MasterEvarior/plantochi/docs/images/dump/20260617_101139.jpg

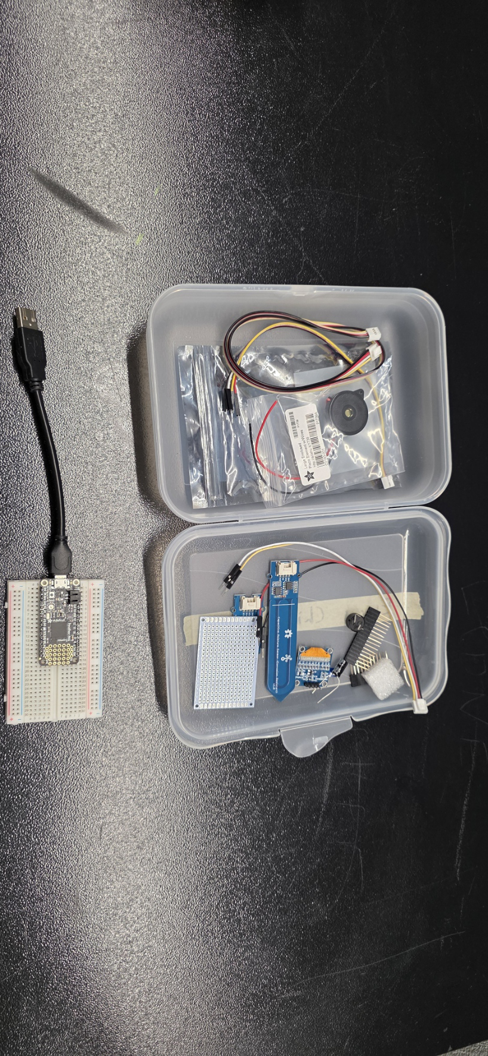
docs/images/dump/20260617_101139.jpg
