MasterEvarior/plantochi/docs/images/dump/20260617_101227.jpg

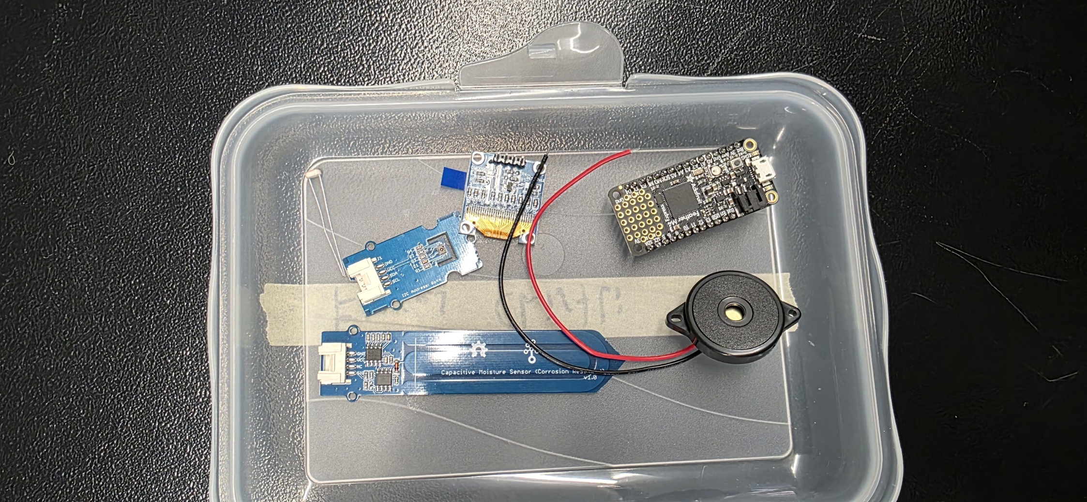
docs/images/dump/20260617_101227.jpg
