MasterEvarior/plantochi/docs/images/dump/20260617_132728.jpg

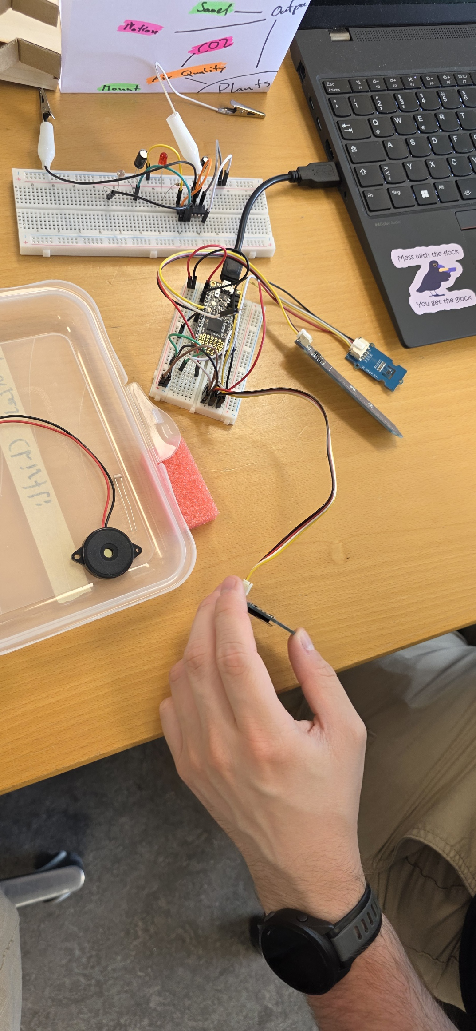
docs/images/dump/20260617_132728.jpg
