MasterEvarior/plantochi/docs/images/dump/20260617_132730.jpg

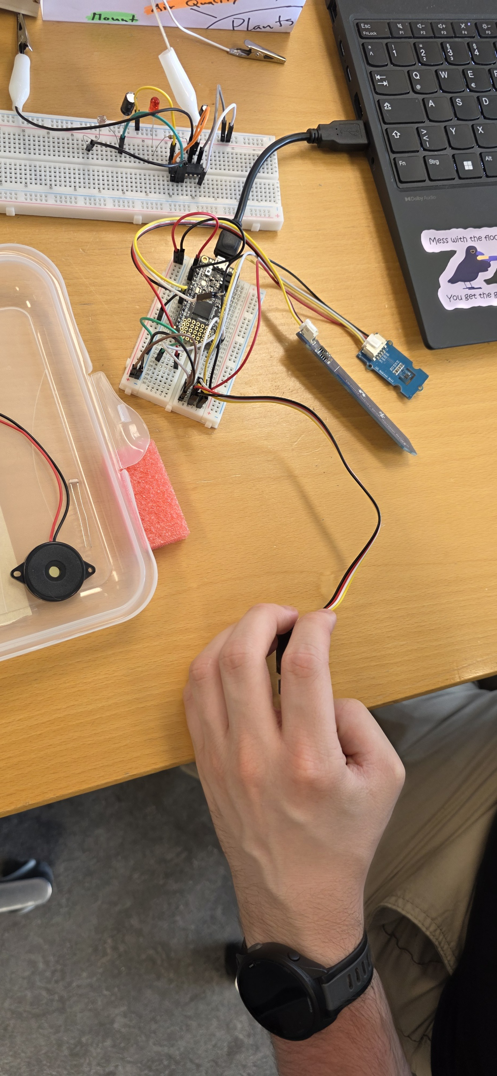
docs/images/dump/20260617_132730.jpg
