MasterEvarior/plantochi/docs/images/dump/20260617_132737.jpg

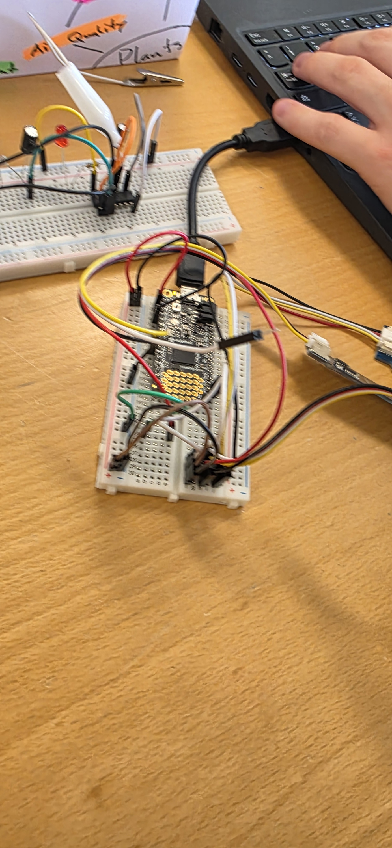
docs/images/dump/20260617_132737.jpg
