MasterEvarior/plantochi/docs/images/dump/20260617_132742.jpg

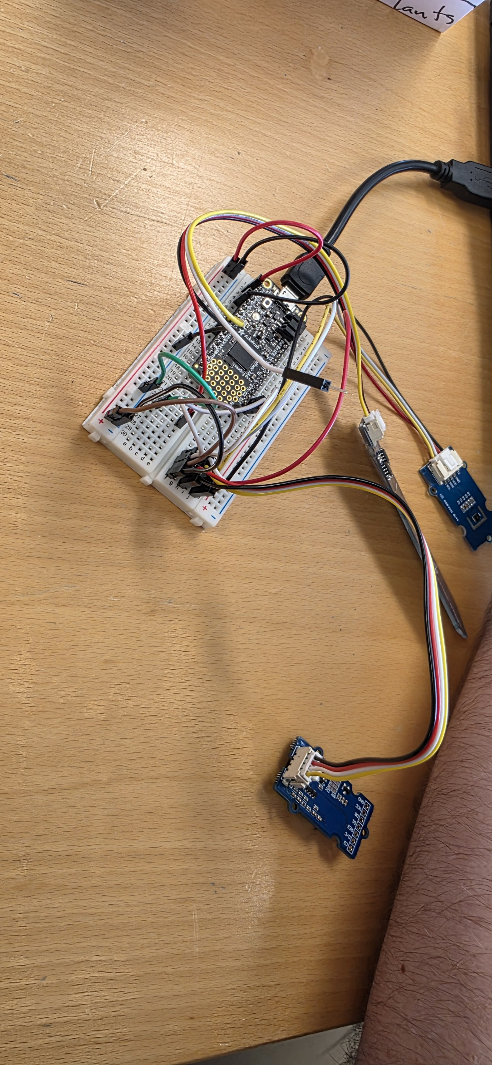
docs/images/dump/20260617_132742.jpg
