MasterEvarior/plantochi/docs/images/dump/20260617_134502.jpg

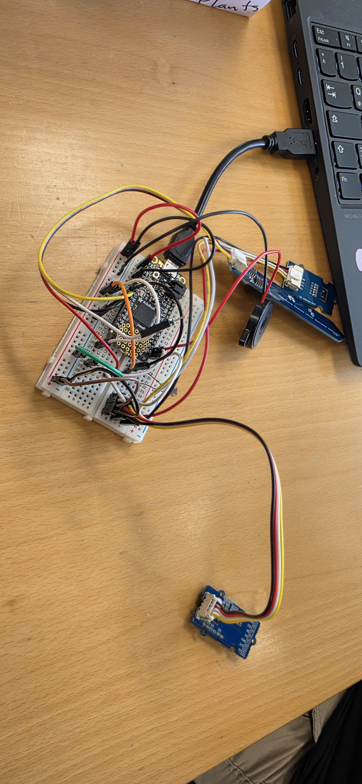
docs/images/dump/20260617_134502.jpg
