MasterEvarior/plantochi/docs/images/dump/20260617_134507.jpg

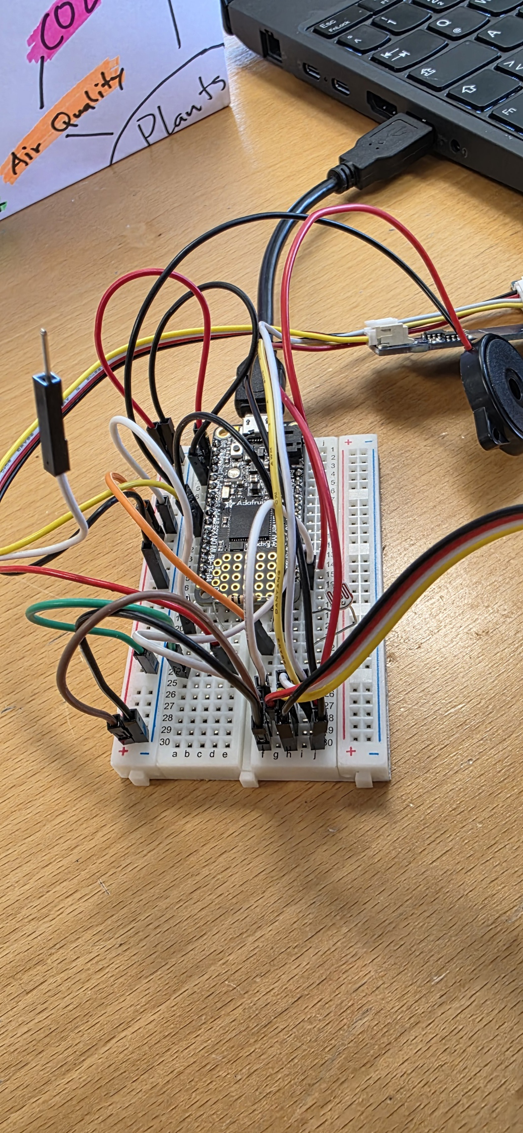
docs/images/dump/20260617_134507.jpg
