MasterEvarior/plantochi/docs/images/dump/20260617_134511.jpg

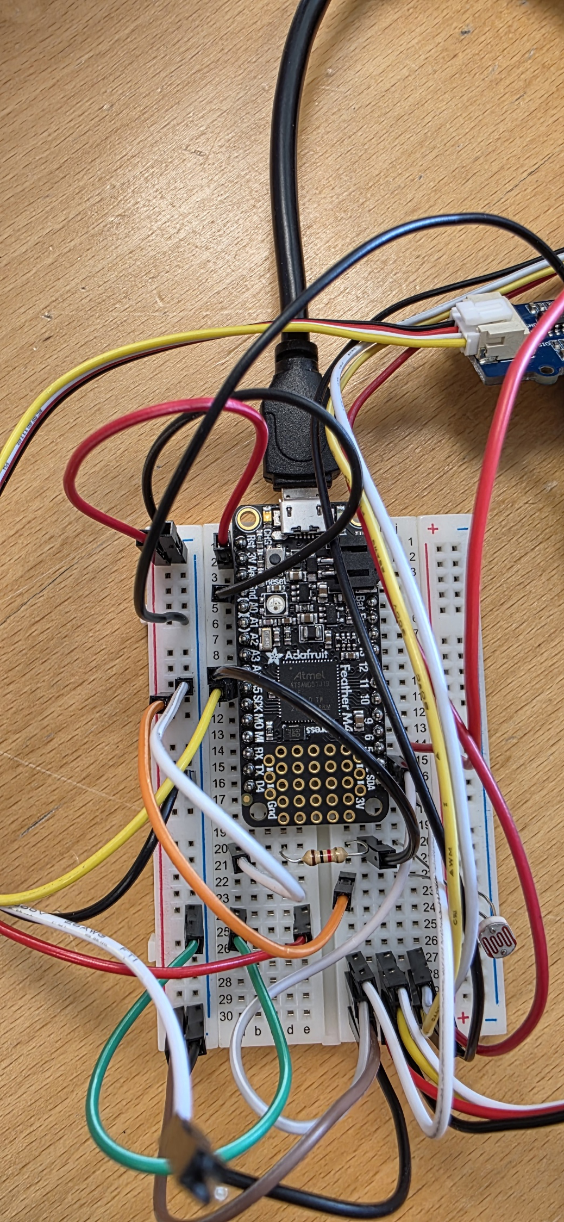
docs/images/dump/20260617_134511.jpg
