MasterEvarior/plantochi/docs/images/dump/20260617_134513.jpg

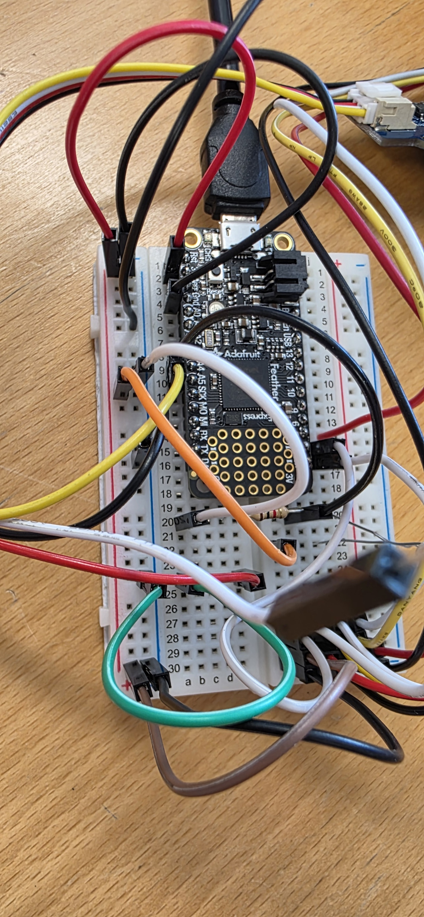
docs/images/dump/20260617_134513.jpg
